IQTLabs/satcom-relay/satcom-relay/sleepmanager.h

volatile uint32_t _awakeTimer = 0;

void setupInterruptSleep(byte pin, void (*isr)(void)) {
  // whenever we get an interrupt, reset the awake clock.
  attachInterrupt(digitalPinToInterrupt(pin), isr, CHANGE);
  // Set external 32k oscillator to run when idle or sleep mode is chosen
  SYSCTRL->XOSC32K.reg |=  (SYSCTRL_XOSC32K_RUNSTDBY | SYSCTRL_XOSC32K_ONDEMAND);
  REG_GCLK_CLKCTRL  |= GCLK_CLKCTRL_ID(GCM_EIC) | // generic clock multiplexer id for the external interrupt controller
                       GCLK_CLKCTRL_GEN_GCLK1 |   // generic clock 1 which is xosc32k
                       GCLK_CLKCTRL_CLKEN;        // enable it
  // Write protected, wait for sync
  while (GCLK->STATUS.bit.SYNCBUSY);

  // Set External Interrupt Controller to use channel 4
  EIC->WAKEUP.reg |= EIC_WAKEUP_WAKEUPEN4;

  PM->SLEEP.reg |= PM_SLEEP_IDLE_CPU;  // Enable Idle0 mode - sleep CPU clock only
  //PM->SLEEP.reg |= PM_SLEEP_IDLE_AHB; // Idle1 - sleep CPU and AHB clocks
  //PM->SLEEP.reg |= PM_SLEEP_IDLE_APB; // Idle2 - sleep CPU, AHB, and APB clocks

  // It is either Idle mode or Standby mode, not both.
  SCB->SCR |= SCB_SCR_SLEEPDEEP_Msk;   // Enable Standby or "deep sleep" mode
}

class SleepManager {
  public:
    SleepManager(byte pin, long int awake_interval) { setupInterruptSleep(pin, this->isr); _awake_interval = awake_interval; };
    bool SleepTime() { return nowTimeDiff(_awakeTimer) > _awake_interval; };
    void WFI() { __WFI(); } // wake from interrupt
    static void isr() { _awakeTimer = millis(); };
    long int _awake_interval = 0;
};
